Solene49000/Station_Meteo_2022-2023/Codes/Dernière_version/test_sleep/definition.h

//PROJET STATION METEO
//AMBRE ALLOUIS - SOLENE GUILLAUME
//ANNEE 2022-2023

// *** Variable Lora *****************************//
//define the pins used by the LoRa transceiver module
#define SCK 18 // 22
#define MISO 19
#define MOSI 23
#define SS 5 //ou 4
#define RST 14
#define DI0 26

// *** Variable Fonction  *****************************//
//Viable defini
#define MEASURE 13
//Taille payload
#define PAYLOAD_LEN 17
